asankaSovis/Project-Prometheus-v2.0/Enclosure/Assembly_View_05.jpeg

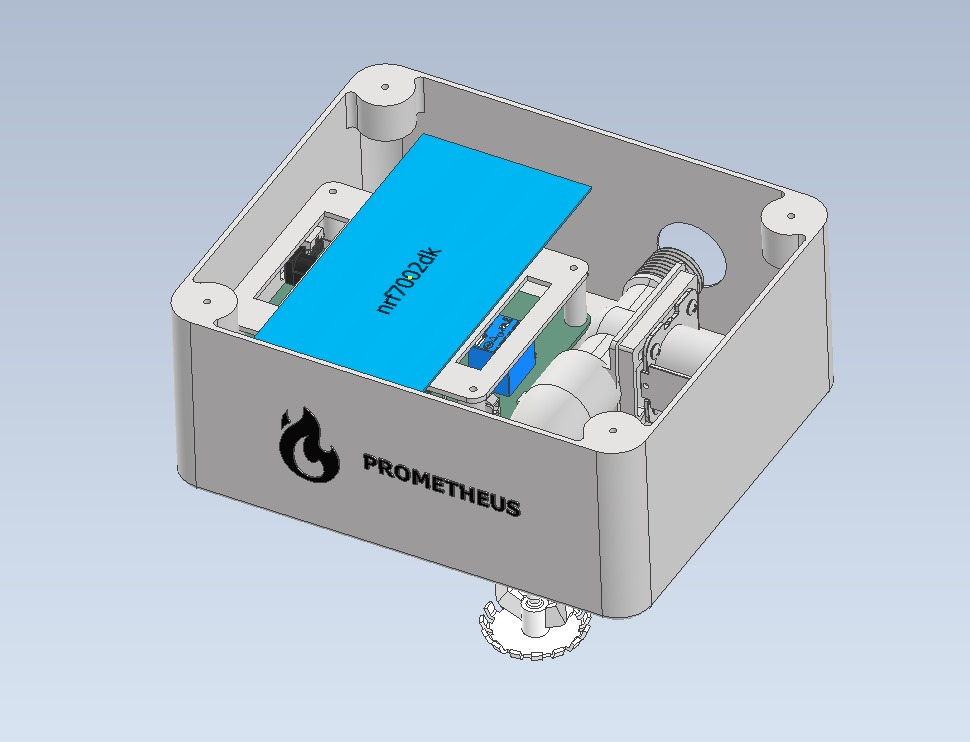
Enclosure/Assembly_View_05.jpeg
