asankaSovis/Project-Prometheus-v2.0/Enclosure/Assembly_View_08.png

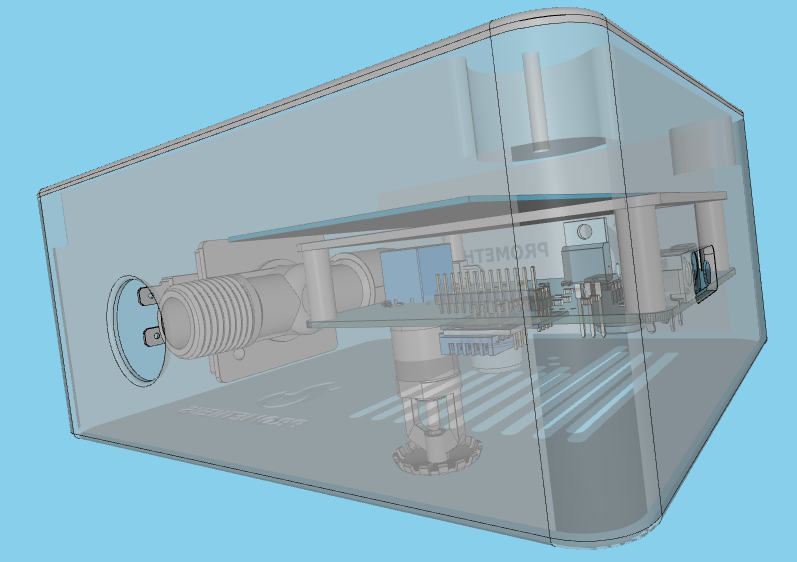
Enclosure/Assembly_View_08.png
